luksab/keychordz/ESP32/main/ble_import.c

#include <stdio.h>
#include <stdlib.h>
#include <string.h>
#include "freertos/FreeRTOS.h"
#include "freertos/task.h"
#include "freertos/event_groups.h"
#include "esp_system.h"
#include "esp_wifi.h"
#include "esp_event.h"
#include "esp_log.h"
#include "nvs_flash.h"
#include "esp_bt.h"

#include "esp_hidd_prf_api.h"
#include "esp_bt_defs.h"
#include "esp_gap_ble_api.h"
#include "esp_gatts_api.h"
#include "esp_gatt_defs.h"
#include "esp_bt_main.h"
#include "esp_bt_device.h"
#include "driver/gpio.h"
#include "hid_dev.h"

/**
 * Brief:
 * This example Implemented BLE HID device profile related functions, in which the HID device
 * has 4 Reports (1 is mouse, 2 is keyboard and LED, 3 is Consumer Devices, 4 is Vendor devices).
 * Users can choose different reports according to their own application scenarios.
 * BLE HID profile inheritance and USB HID class.
 */

/** 
 * Note:
 * 1. Win10 does not support vendor report , So SUPPORT_REPORT_VENDOR is always set to FALSE, it defines in hidd_le_prf_int.h
 * 2. Update connection parameters are not allowed during iPhone HID encryption, slave turns 
 * off the ability to automatically update connection parameters during encryption.
 * 3. After our HID device is connected, the iPhones write 1 to the Report Characteristic Configuration Descriptor, 
 * even if the HID encryption is not completed. This should actually be written 1 after the HID encryption is completed.
 * we modify the permissions of the Report Characteristic Configuration Descriptor to `ESP_GATT_PERM_READ | ESP_GATT_PERM_WRITE_ENCRYPTED`.
 * if you got `GATT_INSUF_ENCRYPTION` error, please ignore.
 */

#define HID_DEMO_TAG "HID_DEMO"

static uint16_t hid_conn_id = 0;
static bool sec_conn = false;
static bool send_volum_up = false;
#define CHAR_DECLARATION_SIZE (sizeof(uint8_t))

static void hidd_event_callback(esp_hidd_cb_event_t event, esp_hidd_cb_param_t *param);

#define HIDD_DEVICE_NAME "HID"
static uint8_t hidd_service_uuid128[] = {
    /* LSB <--------------------------------------------------------------------------------> MSB */
    //first uuid, 16bit, [12],[13] is the value
    0xfb,
    0x34,
    0x9b,
    0x5f,
    0x80,
    0x00,
    0x00,
    0x80,
    0x00,
    0x10,
    0x00,
    0x00,
    0x12,
    0x18,
    0x00,
    0x00,
};

static esp_ble_adv_data_t hidd_adv_data = {
    .set_scan_rsp = false,
    .include_name = true,
    .include_txpower = true,
    .min_interval = 0x0006, //slave connection min interval, Time = min_interval * 1.25 msec
    .max_interval = 0x0010, //slave connection max interval, Time = max_interval * 1.25 msec
    .appearance = 0x03c0,   //HID Generic,
    .manufacturer_len = 0,
    .p_manufacturer_data = NULL,
    .service_data_len = 0,
    .p_service_data = NULL,
    .service_uuid_len = sizeof(hidd_service_uuid128),
    .p_service_uuid = hidd_service_uuid128,
    .flag = 0x6,
};

static esp_ble_adv_params_t hidd_adv_params = {
    .adv_int_min = 0x20,
    .adv_int_max = 0x30,
    .adv_type = ADV_TYPE_IND,
    .own_addr_type = BLE_ADDR_TYPE_PUBLIC,
    //.peer_addr            =
    //.peer_addr_type       =
    .channel_map = ADV_CHNL_ALL,
    .adv_filter_policy = ADV_FILTER_ALLOW_SCAN_ANY_CON_ANY,
};

static void hidd_event_callback(esp_hidd_cb_event_t event, esp_hidd_cb_param_t *param)
{
    switch (event)
    {
    case ESP_HIDD_EVENT_REG_FINISH:
    {
        if (param->init_finish.state == ESP_HIDD_INIT_OK)
        {
            //esp_bd_addr_t rand_addr = {0x04,0x11,0x11,0x11,0x11,0x05};
            esp_ble_gap_set_device_name(HIDD_DEVICE_NAME);
            esp_ble_gap_config_adv_data(&hidd_adv_data);
        }
        break;
    }
    case ESP_BAT_EVENT_REG:
    {
        break;
    }
    case ESP_HIDD_EVENT_DEINIT_FINISH:
        break;
    case ESP_HIDD_EVENT_BLE_CONNECT:
    {
        ESP_LOGI(HID_DEMO_TAG, "ESP_HIDD_EVENT_BLE_CONNECT");
        hid_conn_id = param->connect.conn_id;
        break;
    }
    case ESP_HIDD_EVENT_BLE_DISCONNECT:
    {
        sec_conn = false;
        ESP_LOGI(HID_DEMO_TAG, "ESP_HIDD_EVENT_BLE_DISCONNECT");
        esp_ble_gap_start_advertising(&hidd_adv_params);
        break;
    }
    case ESP_HIDD_EVENT_BLE_VENDOR_REPORT_WRITE_EVT:
    {
        ESP_LOGI(HID_DEMO_TAG, "%s, ESP_HIDD_EVENT_BLE_VENDOR_REPORT_WRITE_EVT", __func__);
        ESP_LOG_BUFFER_HEX(HID_DEMO_TAG, param->vendor_write.data, param->vendor_write.length);
    }
    default:
        break;
    }
    return;
}

static void gap_event_handler(esp_gap_ble_cb_event_t event, esp_ble_gap_cb_param_t *param)
{
    switch (event)
    {
    case ESP_GAP_BLE_ADV_DATA_SET_COMPLETE_EVT:
        esp_ble_gap_start_advertising(&hidd_adv_params);
        break;
    case ESP_GAP_BLE_SEC_REQ_EVT:
        for (int i = 0; i < ESP_BD_ADDR_LEN; i++)
        {
            ESP_LOGD(HID_DEMO_TAG, "%x:", param->ble_security.ble_req.bd_addr[i]);
        }
        esp_ble_gap_security_rsp(param->ble_security.ble_req.bd_addr, true);
        break;
    case ESP_GAP_BLE_AUTH_CMPL_EVT:
        sec_conn = true;
        esp_bd_addr_t bd_addr;
        memcpy(bd_addr, param->ble_security.auth_cmpl.bd_addr, sizeof(esp_bd_addr_t));
        ESP_LOGI(HID_DEMO_TAG, "remote BD_ADDR: %08x%04x",
                 (bd_addr[0] << 24) + (bd_addr[1] << 16) + (bd_addr[2] << 8) + bd_addr[3],
                 (bd_addr[4] << 8) + bd_addr[5]);
        ESP_LOGI(HID_DEMO_TAG, "address type = %d", param->ble_security.auth_cmpl.addr_type);
        ESP_LOGI(HID_DEMO_TAG, "pair status = %s", param->ble_security.auth_cmpl.success ? "success" : "fail");
        if (!param->ble_security.auth_cmpl.success)
        {
            ESP_LOGE(HID_DEMO_TAG, "fail reason = 0x%x", param->ble_security.auth_cmpl.fail_reason);
        }
        break;
    default:
        break;
    }
}
