luksab/keychordz/firmware/src/millis.rs

//! from https://github.com/Rahix/avr-hal/blob/main/examples/arduino-uno/src/bin/uno-millis.rs

use core::cell;

// Possible Values:
//
// ╔═══════════╦══════════════╦═══════════════════╗
// ║ PRESCALER ║ TIMER_COUNTS ║ Overflow Interval ║
// ╠═══════════╬══════════════╬═══════════════════╣
// ║        64 ║          250 ║              1 ms ║
// ║       256 ║          125 ║              2 ms ║
// ║       256 ║          250 ║              4 ms ║
// ║      1024 ║          125 ║              8 ms ║
// ║      1024 ║          250 ║             16 ms ║
// ╚═══════════╩══════════════╩═══════════════════╝
const PRESCALER: u32 = 1024;
const TIMER_COUNTS: u32 = 125;

const MILLIS_INCREMENT: u32 = PRESCALER * TIMER_COUNTS / 16000;

static MILLIS_COUNTER: avr_device::interrupt::Mutex<cell::Cell<u32>> =
    avr_device::interrupt::Mutex::new(cell::Cell::new(0));

/// call this once at the start of the program
pub fn millis_init(tc0: arduino_hal::pac::TC0) {
    // Configure the timer for the above interval (in CTC mode)
    // and enable its interrupt.
    tc0.tccr0a.write(|w| w.wgm0().ctc());
    tc0.ocr0a.write(|w| unsafe { w.bits(TIMER_COUNTS as u8) });
    tc0.tccr0b.write(|w| match PRESCALER {
        8 => w.cs0().prescale_8(),
        64 => w.cs0().prescale_64(),
        256 => w.cs0().prescale_256(),
        1024 => w.cs0().prescale_1024(),
        _ => panic!(),
    });
    tc0.timsk0.write(|w| w.ocie0a().set_bit());

    // Reset the global millisecond counter
    avr_device::interrupt::free(|cs| {
        MILLIS_COUNTER.borrow(cs).set(0);
    });
}

#[avr_device::interrupt(atmega32u4)]
fn TIMER0_COMPA() {
    avr_device::interrupt::free(|cs| {
        let counter_cell = MILLIS_COUNTER.borrow(cs);
        let counter = counter_cell.get();
        counter_cell.set(counter + MILLIS_INCREMENT);
    })
}

/// get the number of milliseconds since the `millis_init` was called
pub fn millis() -> u32 {
    avr_device::interrupt::free(|cs| MILLIS_COUNTER.borrow(cs).get())
}
